gyuha/fixed-angled-drawer/output/w70-wall2.4/module3.stl

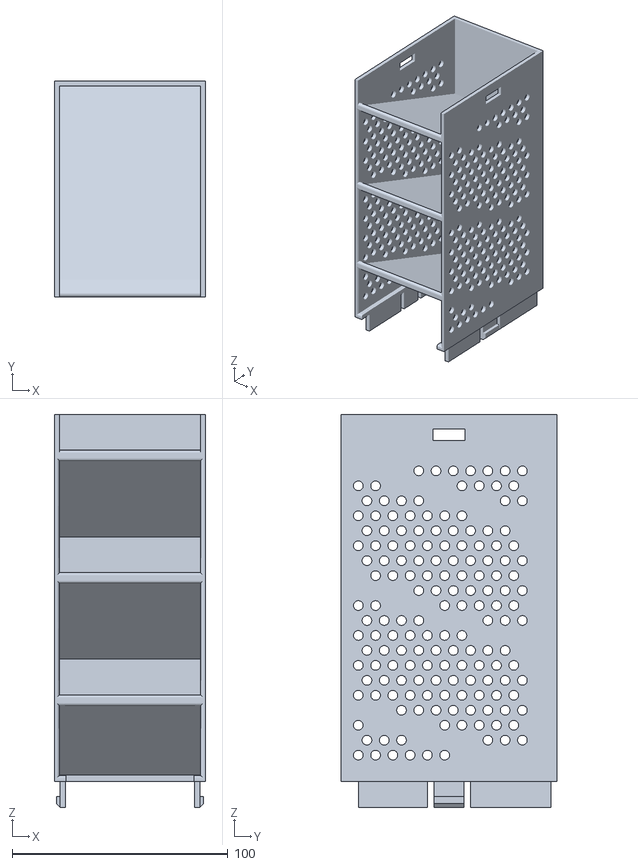
[picture p20: CAD file, 2026-08-21]
output/w70-wall2.4/module3.stl
70.0 x 100.0 x 182.0
