gyuha/fixed-angled-drawer/output/w80-wall2.4/module3.stl

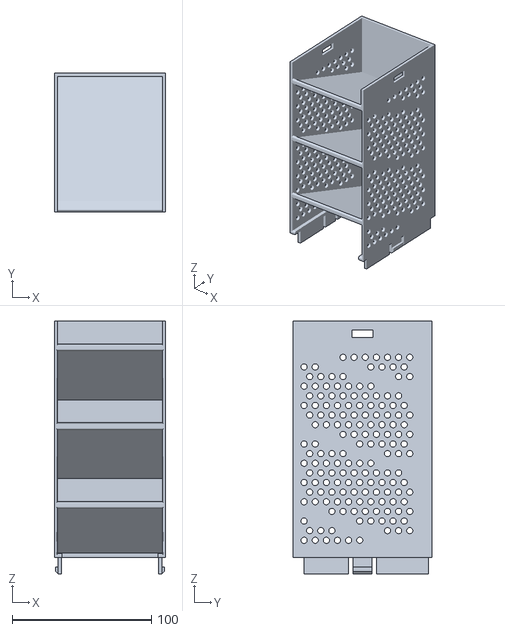
[picture p21: CAD file, 2026-08-21]
output/w80-wall2.4/module3.stl
80.0 x 100.0 x 182.0
