gyuha/fixed-angled-drawer/output/w80-wall3.0/fixed-drawer.3mf

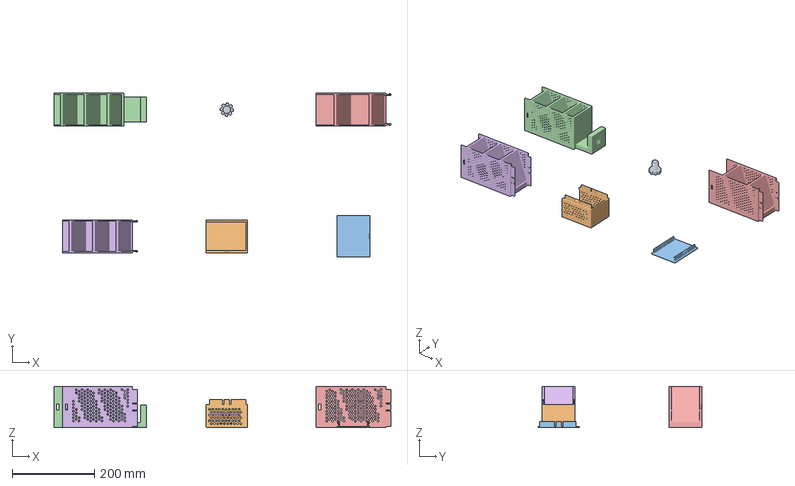
[picture p22: CAD file, 2026-08-17]
output/w80-wall3.0/fixed-drawer.3mf
817.4 x 397.2 x 100.0 mm
thumbscrew.stl
topmodule.stl
lid.stl
tier1.stl
module2.stl
module3.stl
