gyuha/fixed-angled-drawer/output/w70-wall2.4/topmodule.stl

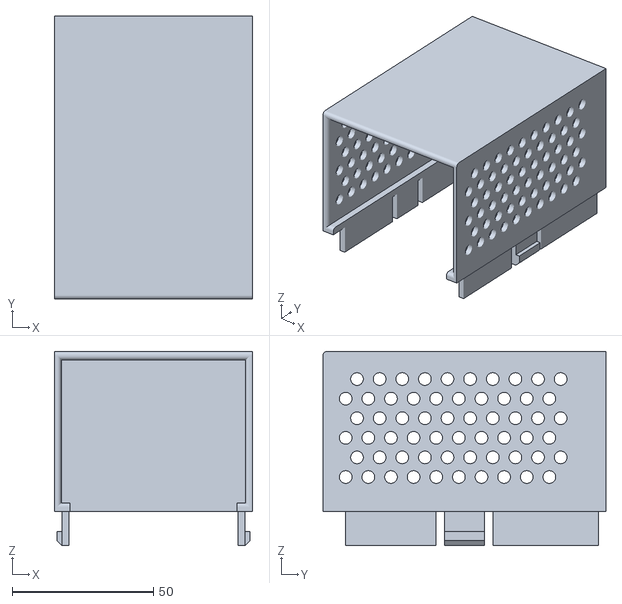
[picture p23: CAD file, 2026-08-21]
output/w70-wall2.4/topmodule.stl
70.0 x 100.0 x 68.7
