gyuha/fixed-angled-drawer/output/w80-wall3.0/topmodule.stl

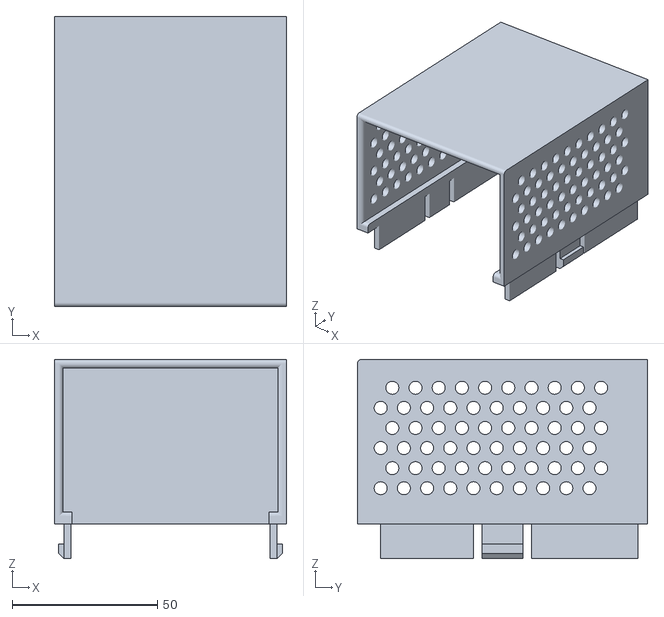
[picture p24: CAD file, 2026-08-17]
output/w80-wall3.0/topmodule.stl
80.0 x 100.0 x 68.7
