gyuha/fixed-angled-drawer/output/w80-wall2.4/topmodule.stl

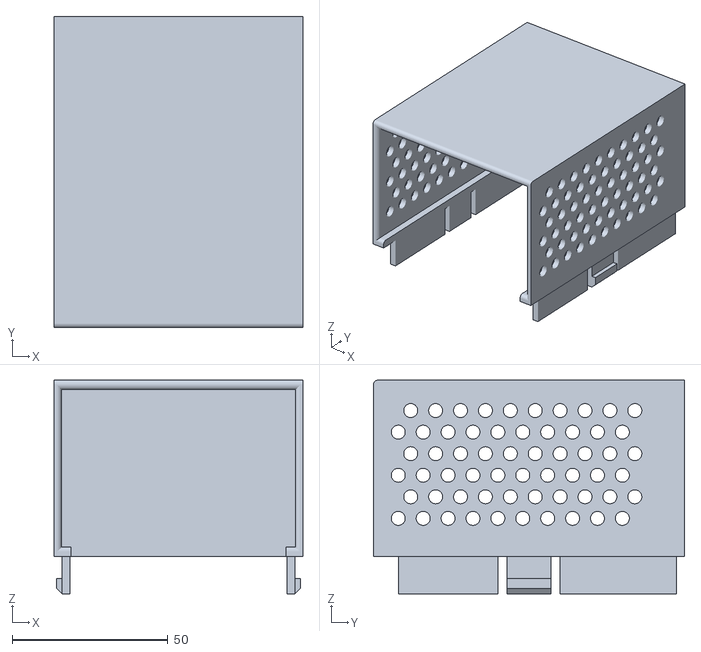
[picture p25: CAD file, 2026-08-21]
output/w80-wall2.4/topmodule.stl
80.0 x 100.0 x 68.7
