gyuha/fixed-angled-drawer/output/w70-wall2.4/fixed-drawer.3mf

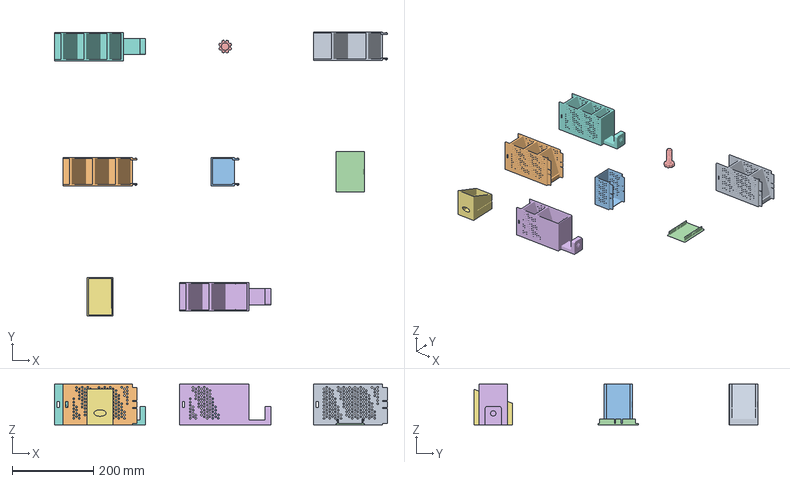
[picture p26: CAD file, 2026-08-21]
output/w70-wall2.4/fixed-drawer.3mf
817.8 x 697.9 x 100.0 mm
module2.stl
module3.stl
topmodule.stl
lid.stl
thumbscrew.stl
tier1-drawer.stl
drawer.stl
tier1.stl
