gyuha/fixed-angled-drawer/output/w70-wall3.0/module2.stl

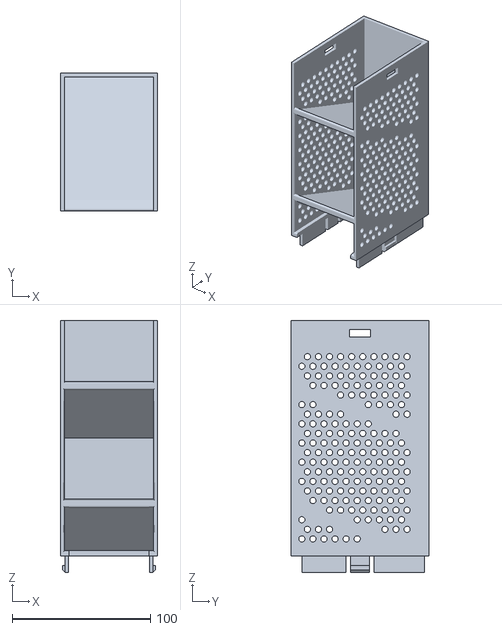
[picture p27: CAD file, 2026-08-17]
output/w70-wall3.0/module2.stl
70.0 x 100.0 x 182.0
